majabojarska/bumble-tuby/amp/amp.kicad_sch

## KiCad design amp/amp.kicad_sch (2025-04-19, an earlier design)

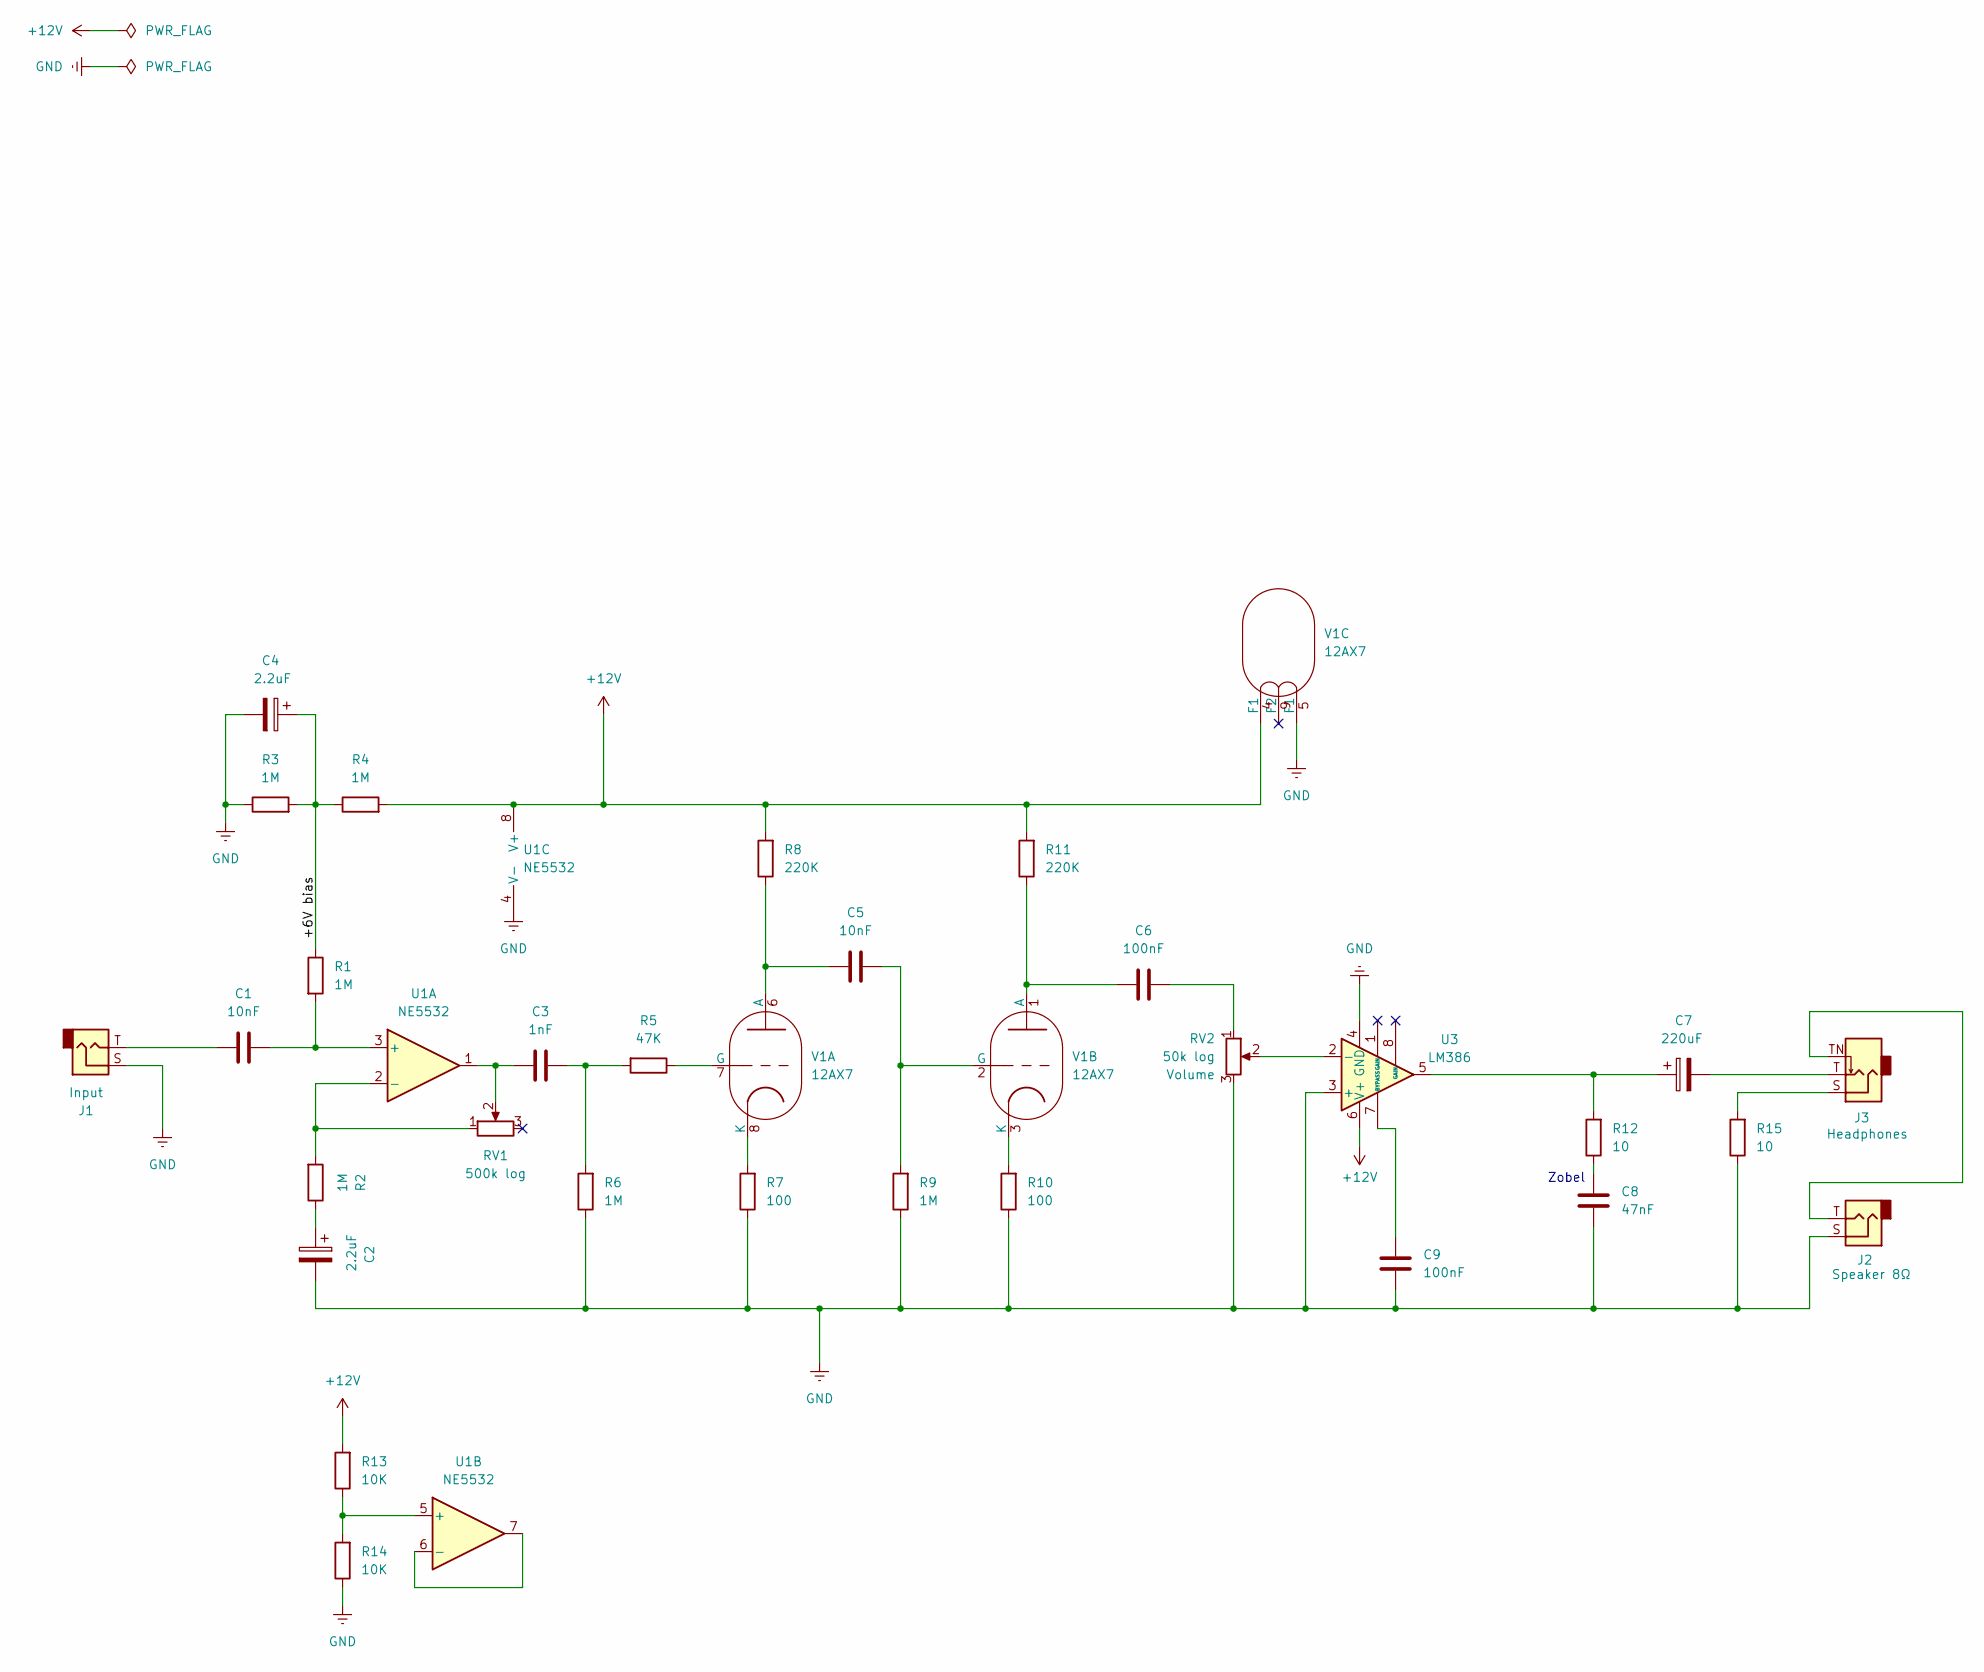
[picture p5: schematic amp.kicad_sch]

Parts:
C1, C5: 10nF
C2, C4: 2.2uF
C3: 1nF
C6, C9: 100nF
C7: 220uF
C8: 47nF
J1: Input
J2: Speaker 8Ω
J3: Headphones
R1, R2, R3, R4, R6, R9: 1M
R5: 47K
R7, R10: 100
R8, R11: 220K
R12, R15: 10
R13, R14: 10K
RV1: 500k log
RV2: 50k log
U1: NE5532
U3: LM386
V1: 12AX7; Valve_Noval_P

Connections:
+6V bias: C4.1, R1.1, R3.2, R4.1
+12V: R4.2, R8.2, R11.2, R13.2, U1.8 (V+), U3.6 (V+), V1.4 (F1)
GND: C2.2, C4.2, C8.1, C9.1, J1.S, J2.S, R3.1, R6.1, R7.1, R9.1, R10.1, R14.1, R15.1, RV2.3, U1.4 (V-), U3.3 (+), U3.4 (GND), V1.5 (F1)
unnamed: C1.1, J1.T
unnamed: C1.2, R1.2, U1.3 (+)
unnamed: C2.1, R2.1
unnamed: C3.1, RV1.2, U1.1
unnamed: C3.2, R5.2, R6.2
unnamed: C5.1, R8.1, V1.6 (A)
unnamed: C5.2, R9.2, V1.2 (G)
unnamed: C6.1, R11.1, V1.1 (A)
unnamed: C6.2, RV2.1
unnamed: C7.1, R12.2, U3.5
unnamed: C7.2, J3.T
unnamed: C8.2, R12.1
unnamed: C9.2, U3.7 (BYPASS)
unnamed: J2.T, J3.TN
unnamed: J3.S, R15.2
unnamed: R2.2, RV1.1, U1.2 (-)
unnamed: R5.1, V1.7 (G)
unnamed: R7.2, V1.8 (K)
unnamed: R10.2, V1.3 (K)
unnamed: R13.1, R14.2, U1.5 (+)
unnamed: RV2.2, U3.2 (-)
unnamed: U1.6 (-), U1.7

Notes on the sheet:
Zobel
